kukela/MyBusinessCard/web/MyBC_admin/test/img/x4.jpg

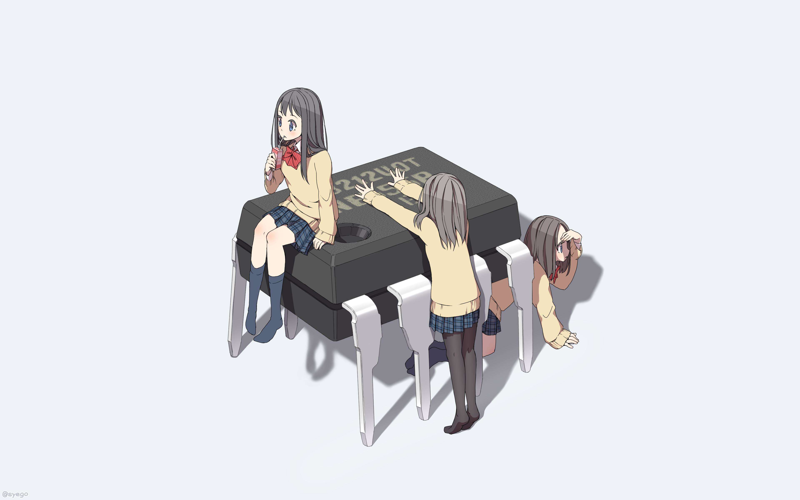
web/MyBC_admin/test/img/x4.jpg
